PraneelBhatia/GameIT-Retro-Gameboy/img/Bench_Supply.png

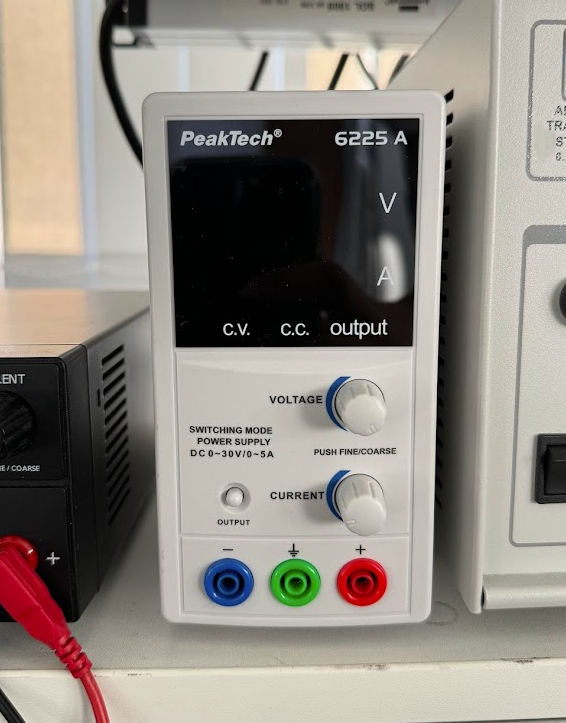
img/Bench_Supply.png
