PraneelBhatia/GameIT-Retro-Gameboy/img/OLED_Trouble.png

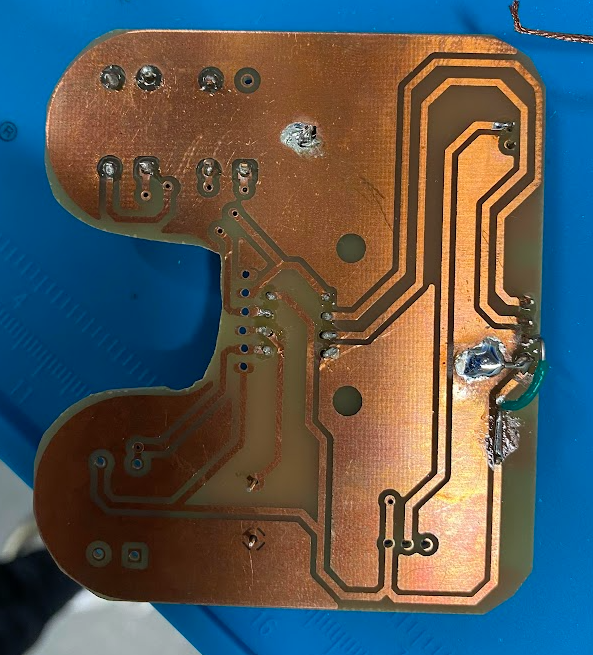
img/OLED_Trouble.png
