PraneelBhatia/GameIT-Retro-Gameboy/img/Placing_on_Copper_Plate.png

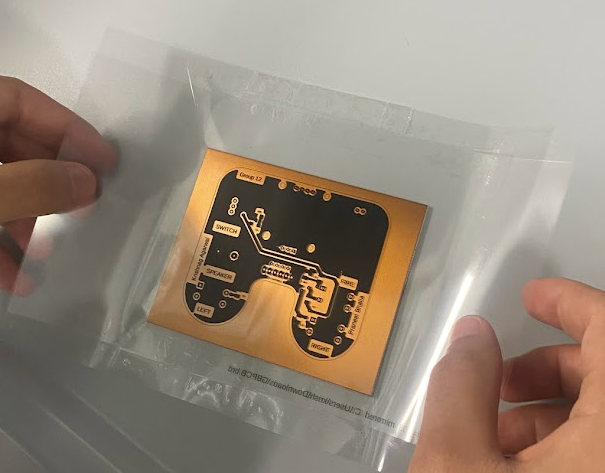
img/Placing_on_Copper_Plate.png
