PraneelBhatia/GameIT-Retro-Gameboy/img/Routing_Final.png

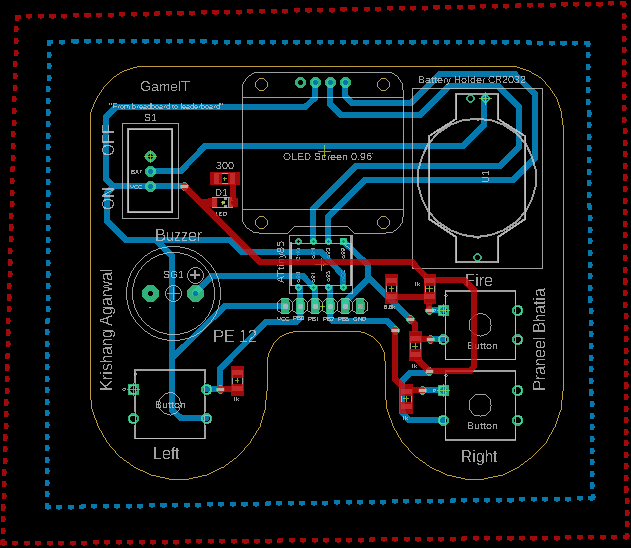
img/Routing_Final.png
