PraneelBhatia/GameIT-Retro-Gameboy/img/Vias_Machine.png

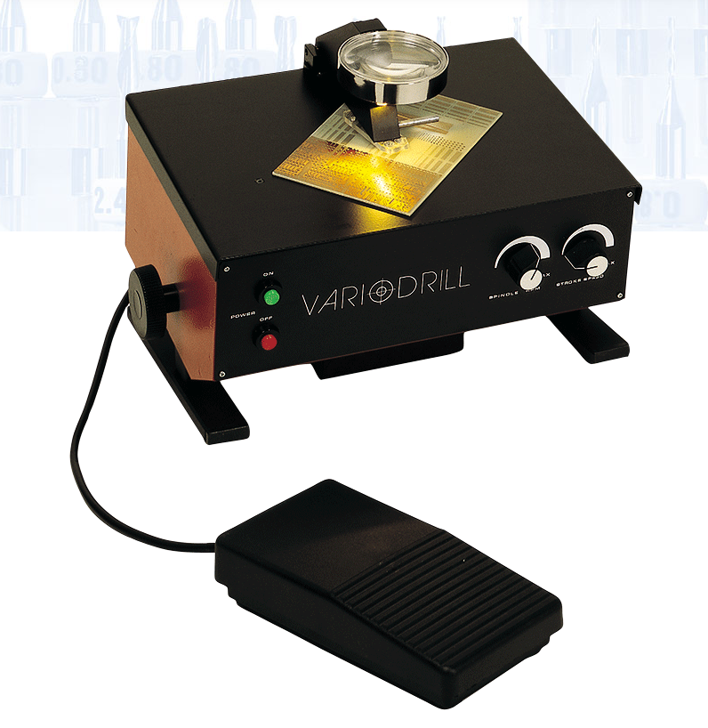
img/Vias_Machine.png
